Mark-MDO47/mdoNotATypeWriter/resources/KiCad/mdoNotATypeWriter/Battery_Power.kicad_sch

## KiCad design resources/KiCad/mdoNotATypeWriter/Battery_Power.kicad_sch (2025-07-31)

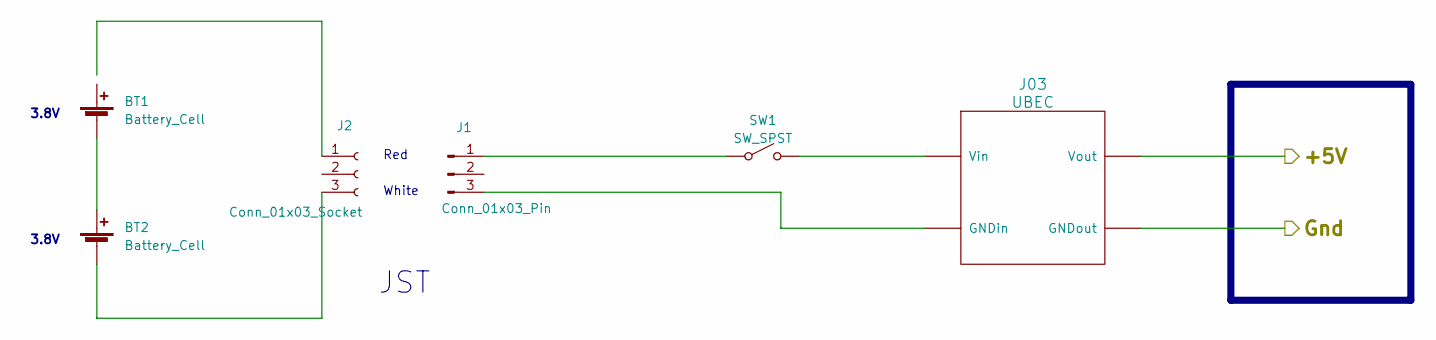
[picture p13: schematic Battery_Power.kicad_sch]

Parts:
BT1, BT2: Battery_Cell
J1: Conn_01x03_Pin
J2: Conn_01x03_Socket
J03: UBEC
SW1: SW_SPST

Connections:
+5V: J03.~
Gnd: J03.~
unnamed: BT1.2 (-), BT2.1 (+)
unnamed: BT2.2 (-), J2.3
unnamed: J1.1, SW1.~
unnamed: J1.3, J03.~, SW1.~

Notes on the sheet:
Red
JST
White
3.8V
