Mark-MDO47/mdoNotATypeWriter/resources/KiCad/mdoNotATypeWriter/mdoNotATypeWriter.kicad_sch

## KiCad design resources/KiCad/mdoNotATypeWriter/mdoNotATypeWriter.kicad_sch (2025-08-16, an earlier design)

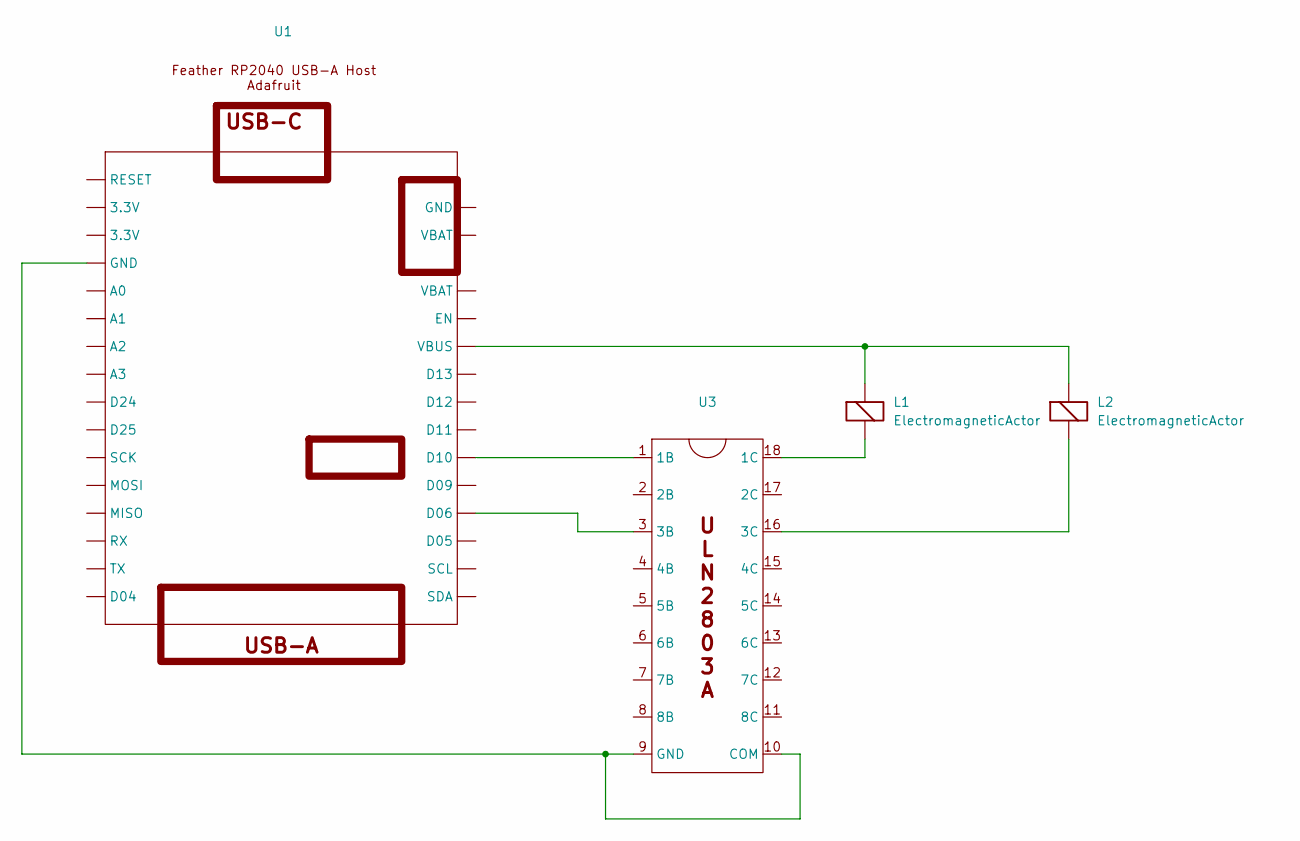
[picture p14: schematic mdoNotATypeWriter.kicad_sch]

Parts:
L1, L2: ElectromagneticActor
U1, U3: (no value)

Connections:
unnamed: L1.1 (-), L2.1 (-), U1.
unnamed: L1.2 (+), U3.18 (1C)
unnamed: L2.2 (+), U3.16 (3C)
unnamed: U1., U3.1 (1B), U3.3 (3B), U3.9 (GND), U3.10 (COM)
